ssbingo/HB-OU-RGB-STACKFIRE/AddOn/usr/local/addons/jp-hb-devices-addon/www/config/img/devices/250/hb-ou-rgb-campfire.png

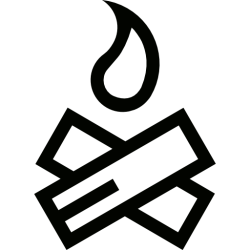
AddOn/usr/local/addons/jp-hb-devices-addon/www/config/img/devices/250/hb-ou-rgb-campfire.png
