ssbingo/HB-OU-RGB-STACKFIRE/Info/Mini Mega 2560_01.jpg

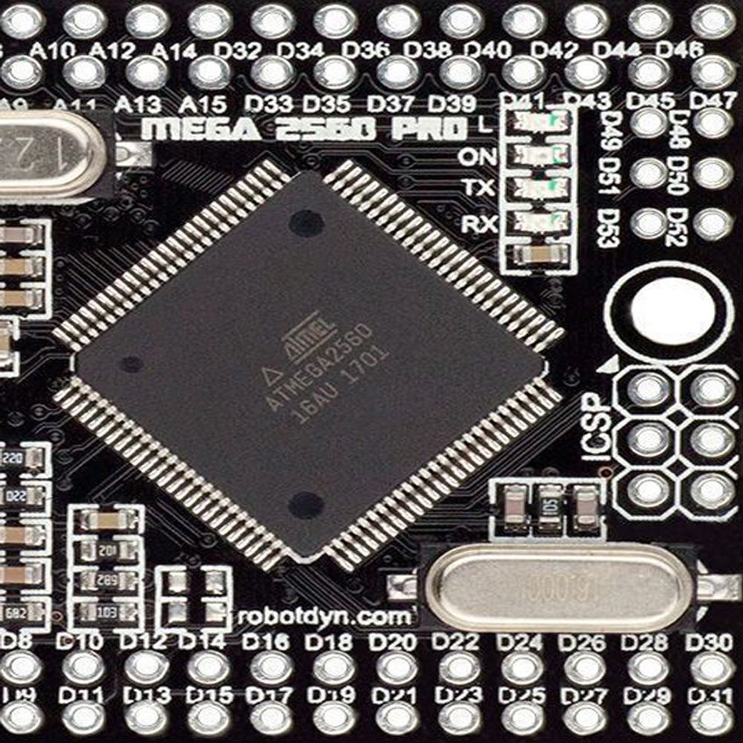
Info/Mini Mega 2560_01.jpg
