ssbingo/HB-OU-RGB-STACKFIRE/Info/Mini Mega 2560_02.jpg

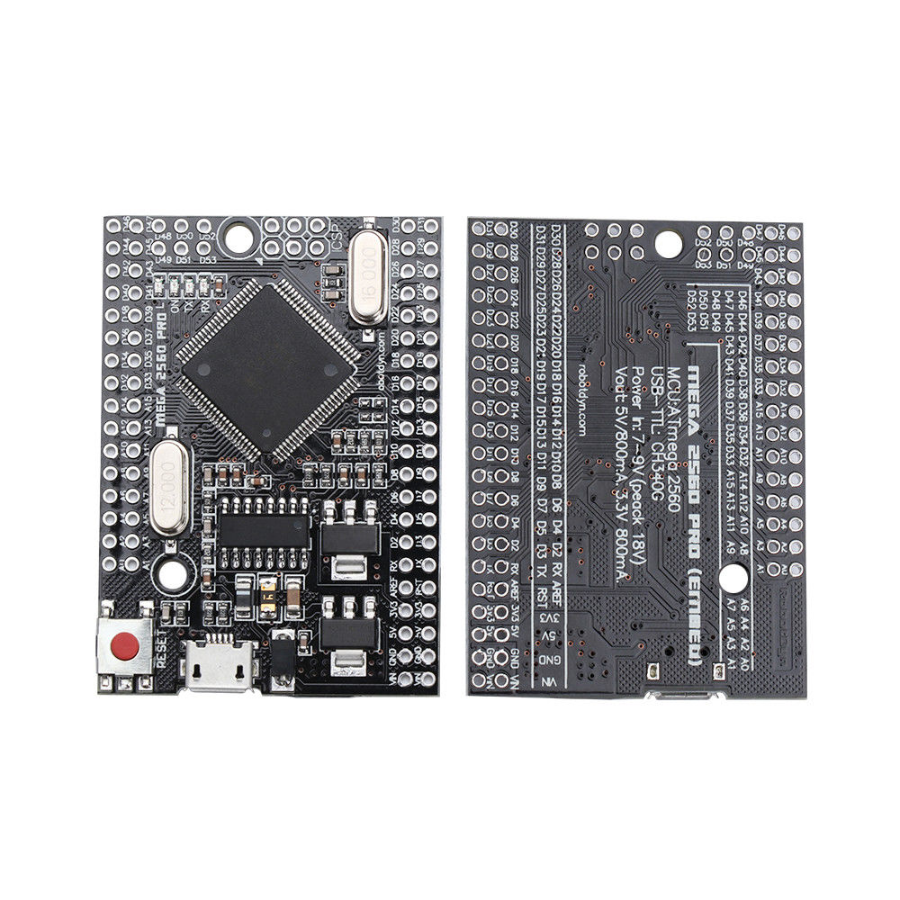
Info/Mini Mega 2560_02.jpg
