ssbingo/HB-OU-RGB-STACKFIRE/Info/s-l1600.jpg

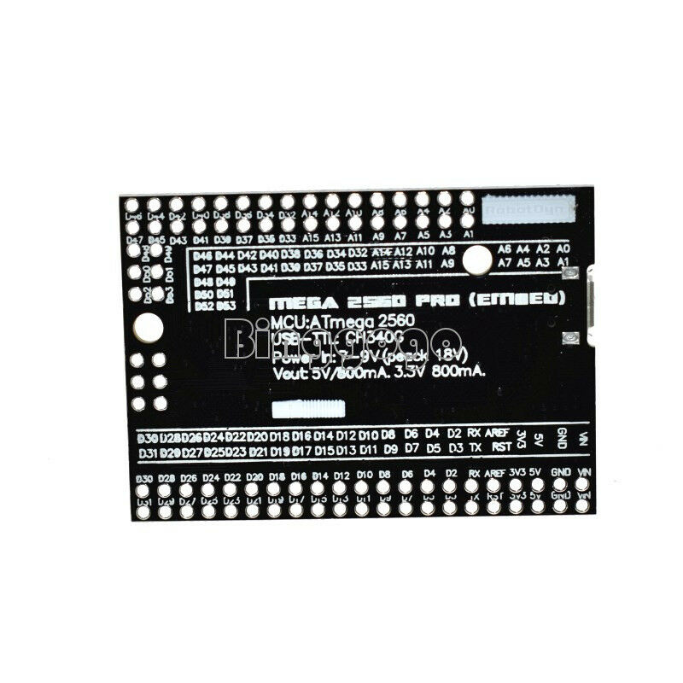
Info/s-l1600.jpg
