ssbingo/HB-OU-RGB-STACKFIRE/Code/HB-OU-RGB-STACKFIRE-V3/RGBProgramsFire.h

#ifndef __RGBPROGRAMSFIRE_H__
#define __RGBPROGRAMSFIRE_H__

CRGBPalette16 gPal;

void RGBProgramFire1(uint8_t brightness, uint8_t PrgNr) {
  
  static unsigned long lastmillis = millis();

  uint8_t COOLING = 0;
  uint8_t SPARKING = 0; 

 switch (PrgNr) {
  case 1:
    COOLING = FIRE_PRG_1_1_COOLING;
    SPARKING = FIRE_PRG_1_1_SPARKING;
    break;    
  case 2:
    COOLING = FIRE_PRG_1_2_COOLING;
    SPARKING = FIRE_PRG_1_2_SPARKING;
    break;    
  case 3:
    COOLING = FIRE_PRG_1_3_COOLING;
    SPARKING = FIRE_PRG_1_3_SPARKING;
    break;    
  case 4:
    COOLING = FIRE_PRG_2_1_COOLING;
    SPARKING = FIRE_PRG_2_1_SPARKING;
    break;    
  case 5:
    COOLING = FIRE_PRG_2_2_COOLING;
    SPARKING = FIRE_PRG_2_2_SPARKING;
    break;    
  case 6:
    COOLING = FIRE_PRG_2_3_COOLING;
    SPARKING = FIRE_PRG_2_3_SPARKING;
    break;        
}

if (GPALNR == 1) {
    static uint8_t hue = 0;
    hue++;
    CRGB darkcolor  = CHSV(hue,255,192); // pure hue, three-quarters brightness
    CRGB lightcolor = CHSV(hue,128,255); // half 'whitened', full brightness
    gPal = CRGBPalette16( CRGB::Black, darkcolor, lightcolor, CRGB::White);
}else if (GPALNR == 2) {
    gPal = CRGBPalette256( CRGB::Black, CRGB::Red, CRGB::OrangeRed, CRGB::Yellow );
}else if (GPALNR == 3) {
    gPal = CRGBPalette16( CRGB::Black, CRGB::Blue, CRGB::Aqua,  CRGB::White);
}else if (GPALNR == 4) {    
    gPal = CRGBPalette16( CRGB::Black, CRGB::Red, CRGB::White);    
}else if (GPALNR == 5) {    
    gPal = RainbowColors_p;
}else if (GPALNR == 6) {    
    gPal = CloudColors_p;
}else if (GPALNR == 7) {    
    gPal = PartyColors_p;
}else if (GPALNR == 8) {    
    gPal = OceanColors_p;
}else if (GPALNR == 9) {    
    gPal = CRGBPalette16( CRGB::Black, CRGB::Red, CRGB::Orange, CRGB::Yellow);  //gPal = ForestColors_p;
}else if (GPALNR == 10) {    
    gPal = HeatColors_p;
}else if (GPALNR == 11) {    
    gPal = LavaColors_p;
}


  if (millis() - lastmillis > 15) {

    static byte heat10[WSNUM_LEDS10];
    static byte heat11[WSNUM_LEDS11];
    static byte heat12[WSNUM_LEDS12];
    static byte heat13[WSNUM_LEDS13];
    static byte heat14[WSNUM_LEDS14];
    static byte heat15[WSNUM_LEDS15];
    static byte heat16[WSNUM_LEDS16];
    static byte heat17[WSNUM_LEDS17];    
    static byte heat18[WSNUM_LEDS18];    
    static byte heat19[WSNUM_LEDS19];    

#ifdef doubleLED
    static byte heat20[WSNUM_LEDS20];  
    static byte heat21[WSNUM_LEDS21];  
    static byte heat22[WSNUM_LEDS22];
    static byte heat23[WSNUM_LEDS23];
    static byte heat24[WSNUM_LEDS24];
    static byte heat25[WSNUM_LEDS25];
    static byte heat26[WSNUM_LEDS26];
    static byte heat27[WSNUM_LEDS27];    
    static byte heat28[WSNUM_LEDS28];      
    static byte heat29[WSNUM_LEDS29];                         
#endif

    for ( int i = 0; i < WSNUM_LEDS10; i++) {
      heat10[i] = qsub8( heat10[i],  random8(0, ((COOLING * 10) / WSNUM_LEDS10) + 2));
    }
    for ( int i = 0; i < WSNUM_LEDS11; i++) {
      heat11[i] = qsub8( heat11[i],  random8(0, ((COOLING * 10) / WSNUM_LEDS11) + 2));
    }
    for ( int i = 0; i < WSNUM_LEDS12; i++) {
      heat12[i] = qsub8( heat12[i],  random8(0, ((COOLING * 10) / WSNUM_LEDS12) + 2));
    }
    for ( int i = 0; i < WSNUM_LEDS13; i++) {
      heat13[i] = qsub8( heat13[i],  random8(0, ((COOLING * 10) / WSNUM_LEDS13) + 2));
    }
    for ( int i = 0; i < WSNUM_LEDS14; i++) {
      heat14[i] = qsub8( heat14[i],  random8(0, ((COOLING * 10) / WSNUM_LEDS14) + 2));
    }
    for ( int i = 0; i < WSNUM_LEDS15; i++) {
      heat15[i] = qsub8( heat15[i],  random8(0, ((COOLING * 10) / WSNUM_LEDS15) + 2));
    }
    for ( int i = 0; i < WSNUM_LEDS16; i++) {
      heat16[i] = qsub8( heat16[i],  random8(0, ((COOLING * 10) / WSNUM_LEDS16) + 2));
    }
    for ( int i = 0; i < WSNUM_LEDS17; i++) {
      heat17[i] = qsub8( heat17[i],  random8(0, ((COOLING * 10) / WSNUM_LEDS17) + 2));
    }                    
    for ( int i = 0; i < WSNUM_LEDS18; i++) {
      heat18[i] = qsub8( heat18[i],  random8(0, ((COOLING * 10) / WSNUM_LEDS18) + 2));
    }                    
    for ( int i = 0; i < WSNUM_LEDS19; i++) {
      heat19[i] = qsub8( heat18[i],  random8(0, ((COOLING * 10) / WSNUM_LEDS19) + 2));
    }                    


#ifdef doubleLED
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

      leds25[pixelnumber] = color;
    }
    
    for ( int j = 0; j < WSNUM_LEDS26; j++) {
      //CRGB color = HeatColor( heat[j]);
      byte colorindex = scale8( heat26[j], 240);
      CRGB color = ColorFromPalette( gPal, colorindex);
      int pixelnumber;

    pixelnumber = j;

      leds26[pixelnumber] = color;
    }
    
    for ( int j = 0; j < WSNUM_LEDS27; j++) {
      //CRGB color = HeatColor( heat[j]);
      byte colorindex = scale8( heat27[j], 240);
      CRGB color = ColorFromPalette( gPal, colorindex);
      int pixelnumber;

    pixelnumber = j;

      leds27[pixelnumber] = color;
    }
    
    for ( int j = 0; j < WSNUM_LEDS28; j++) {
      //CRGB color = HeatColor( heat[j]);
      byte colorindex = scale8( heat28[j], 240);
      CRGB color = ColorFromPalette( gPal, colorindex);
      int pixelnumber;

    pixelnumber = j;

      leds28[pixelnumber] = color;
    }
    
    for ( int j = 0; j < WSNUM_LEDS29; j++) {
      //CRGB color = HeatColor( heat[j]);
      byte colorindex = scale8( heat29[j], 240);
      CRGB color = ColorFromPalette( gPal, colorindex);
      int pixelnumber;

    pixelnumber = j;

      leds29[pixelnumber] = color;
    }
#endif
    lastmillis = millis();
  }
}

#endif
